Rackhamn/Album/img/proto/layout_pv2.jpg

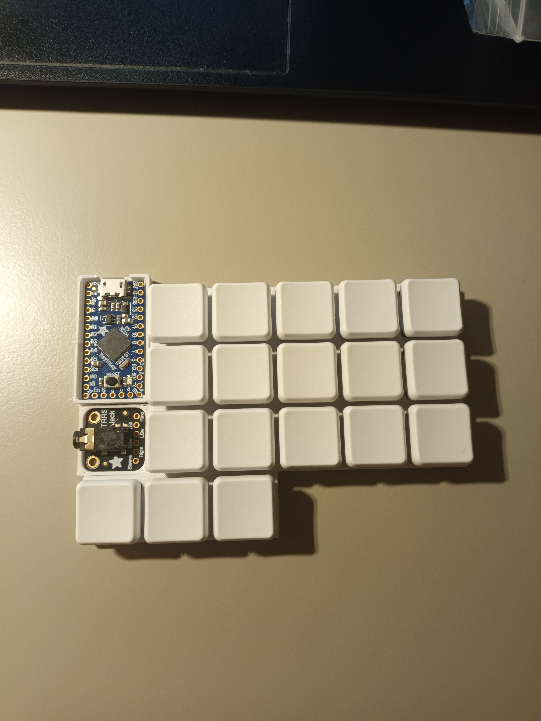
img/proto/layout_pv2.jpg
