Rackhamn/Album/img/proto/layout_pv4.jpg

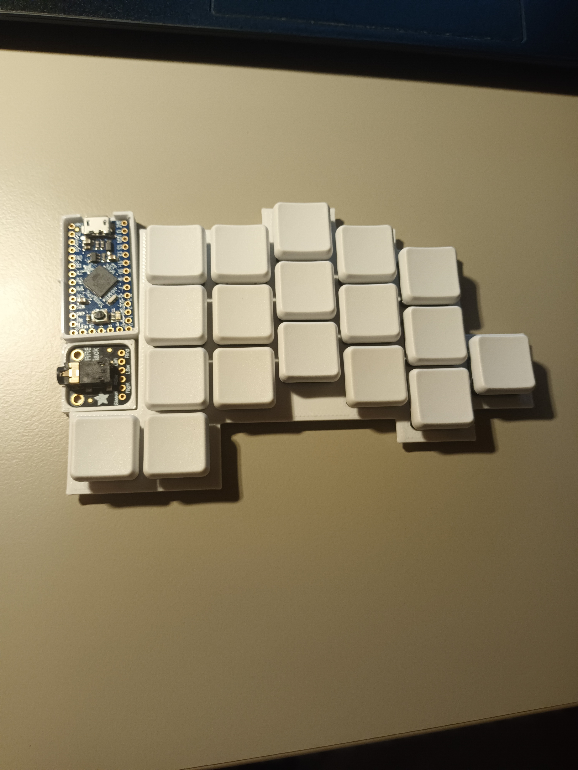
img/proto/layout_pv4.jpg
