Rackhamn/Album/img/proto/keymap_ordering.jpg

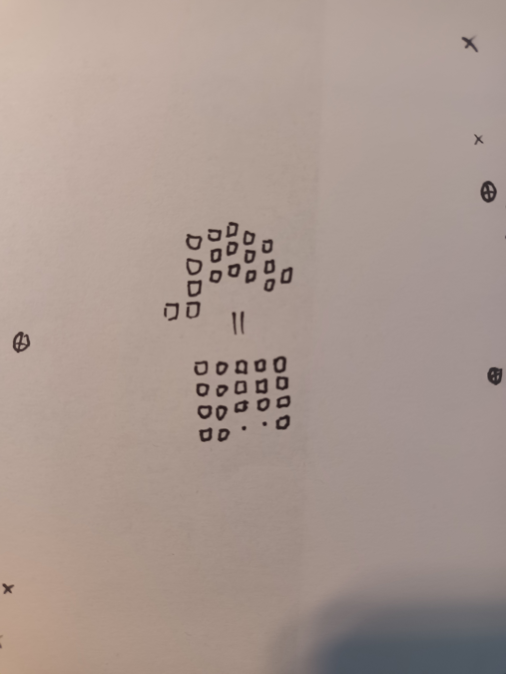
img/proto/keymap_ordering.jpg
