Rackhamn/Album/img/proto/pv4_master_solder.jpg

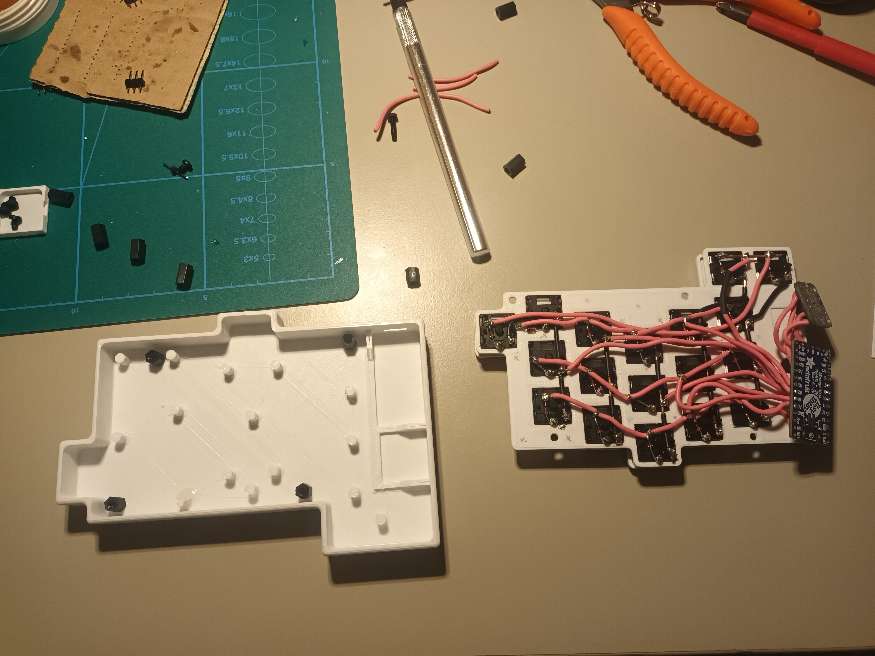
img/proto/pv4_master_solder.jpg
