Rackhamn/Album/img/proto/pv4_slave_solder.jpg

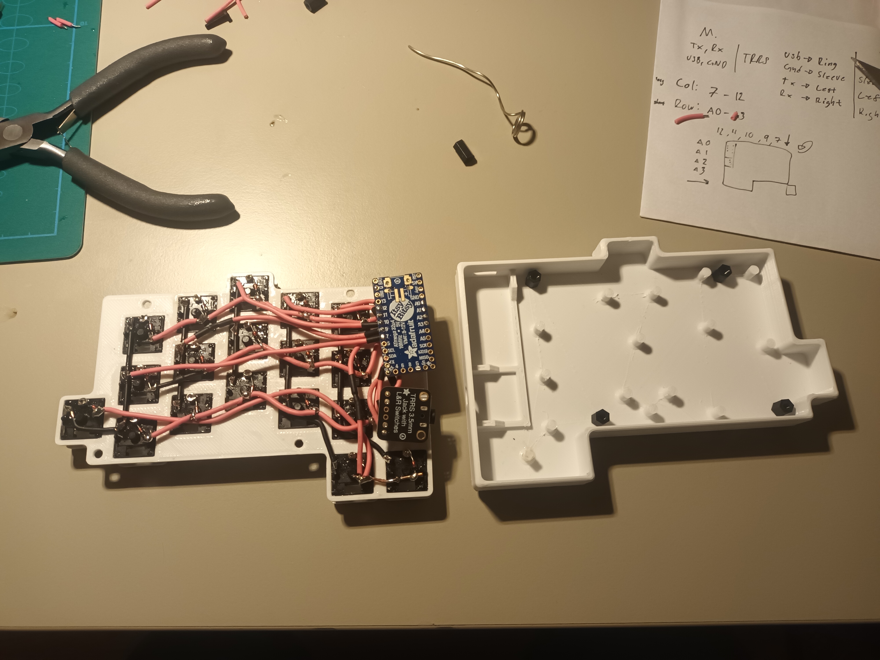
img/proto/pv4_slave_solder.jpg
