Rackhamn/Album/img/proto/pv4_solder1.jpg

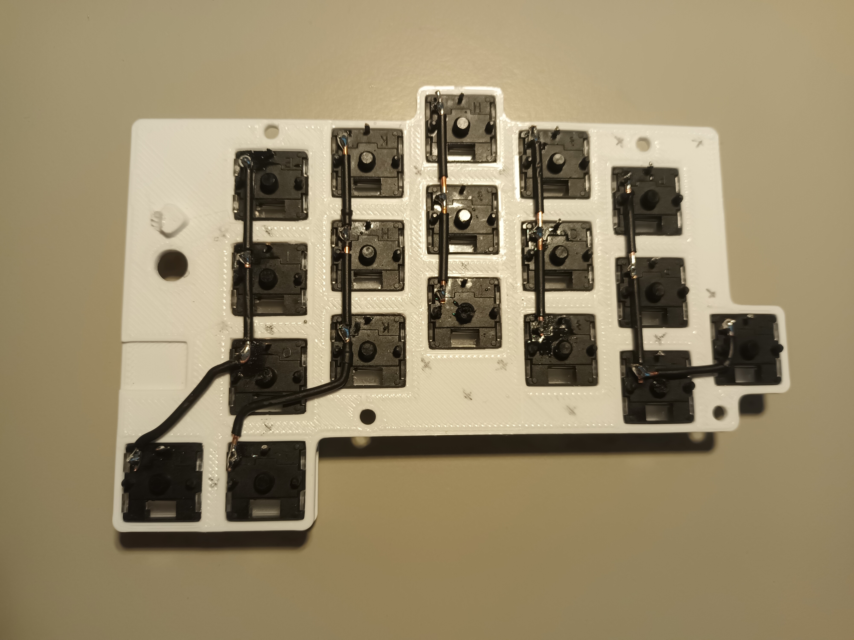
img/proto/pv4_solder1.jpg
