Rackhamn/Album/img/proto/pv4_solder2.jpg

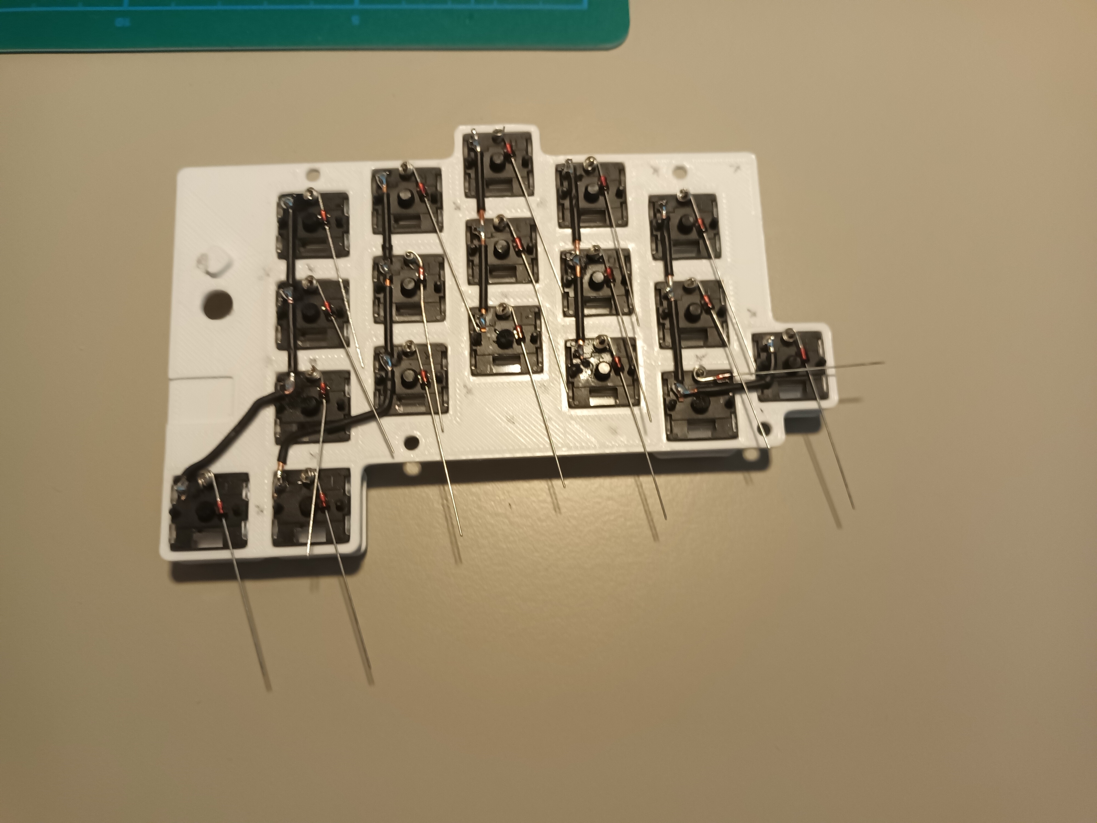
img/proto/pv4_solder2.jpg
