Rackhamn/Album/img/proto/pv4_solder3.jpg

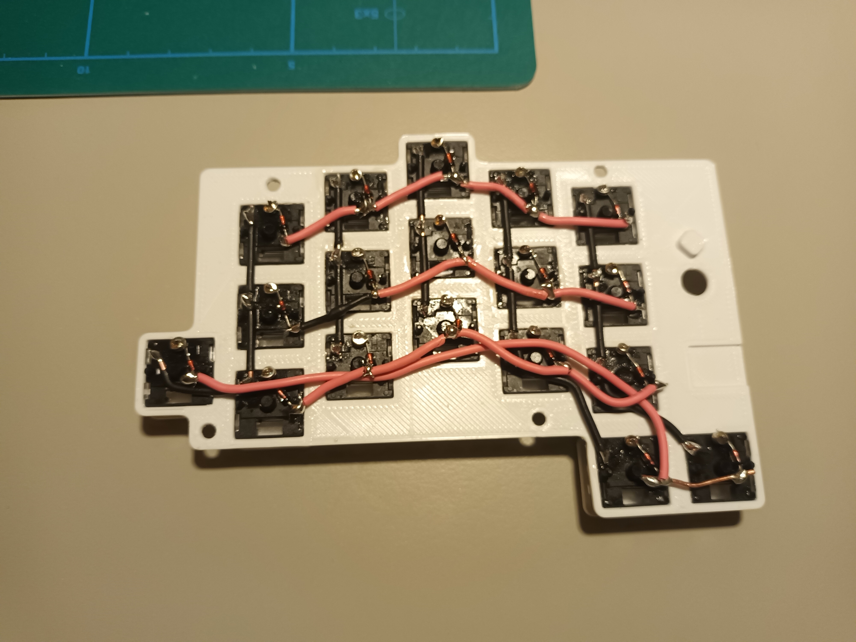
img/proto/pv4_solder3.jpg
