Rackhamn/Album/img/proto/final_case_side_issue.jpg

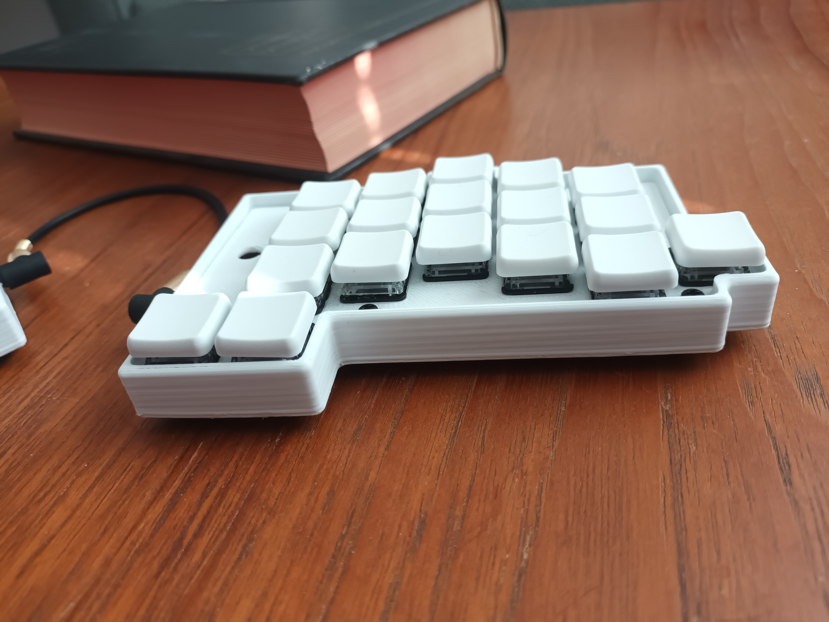
img/proto/final_case_side_issue.jpg
