Rackhamn/Album/src/types.h

#ifndef TYPES_H
#define TYPES_H

#include <stdint.h>

typedef int8_t		i8;
typedef uint8_t 	u8;
typedef int16_t		i16;
typedef uint16_t	u16;
typedef int32_t		i32;
typedef uint32_t	u32;

typedef float		f32;
typedef double		f64;

// maybe not?
#include <stdbool.h>

typedef bool		b1; // is 8
typedef u8			b8;
typedef u16			b16;
typedef u32			b32;

#endif /* TYPES_H */
